PatternAgents/StickSoC/StickSoc/StickSoC_Left/eagleUp/eagleUp_StickSoc_Left_board_bottom.jpg

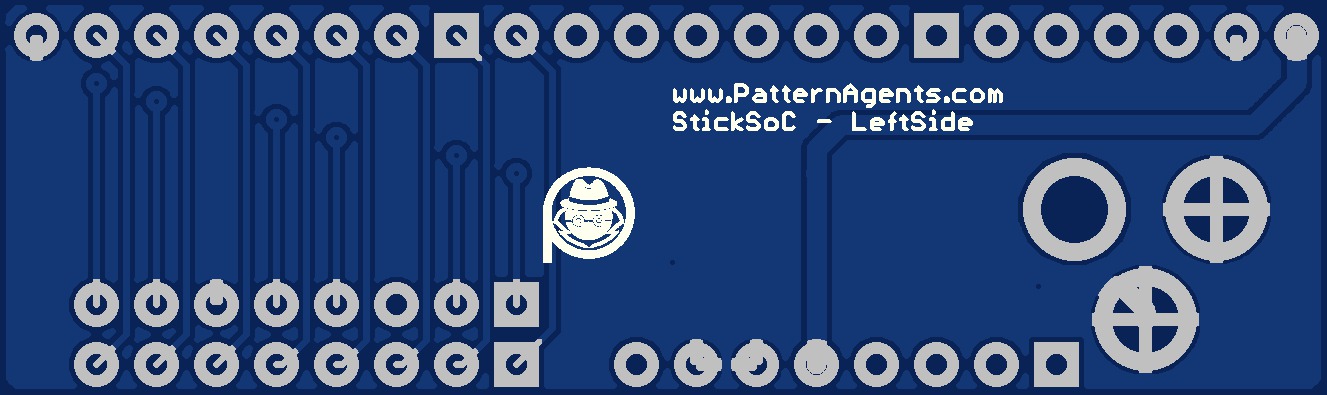
StickSoc/StickSoC_Left/eagleUp/eagleUp_StickSoc_Left_board_bottom.jpg
