PatternAgents/StickSoC/StickSoc/StickSoC_Left/eagleUp/eagleUp_StickSoc_Left_board_top.jpg

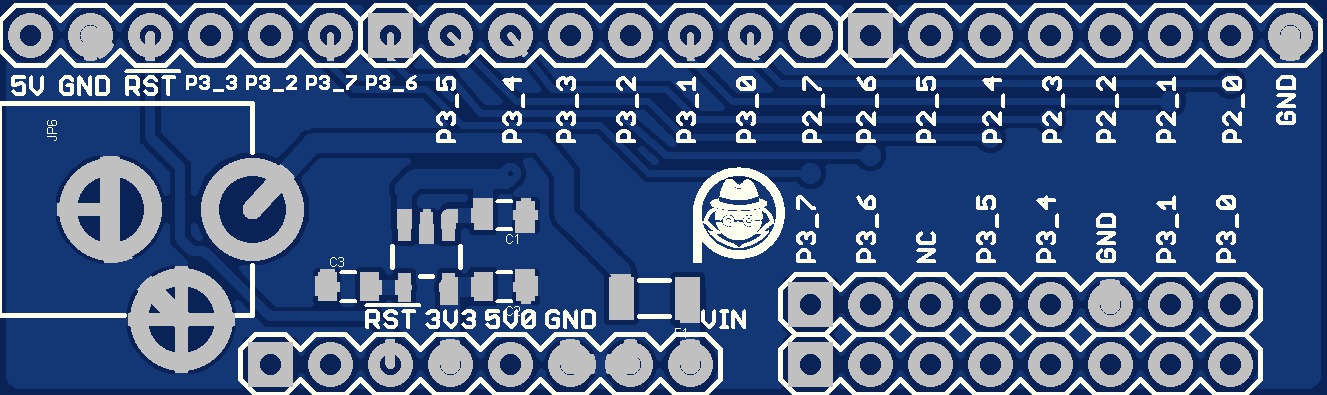
StickSoc/StickSoC_Left/eagleUp/eagleUp_StickSoc_Left_board_top.jpg
