PatternAgents/StickSoC/StickSoc/StickSoC_Left/images/StickSoC_Left_bot.png

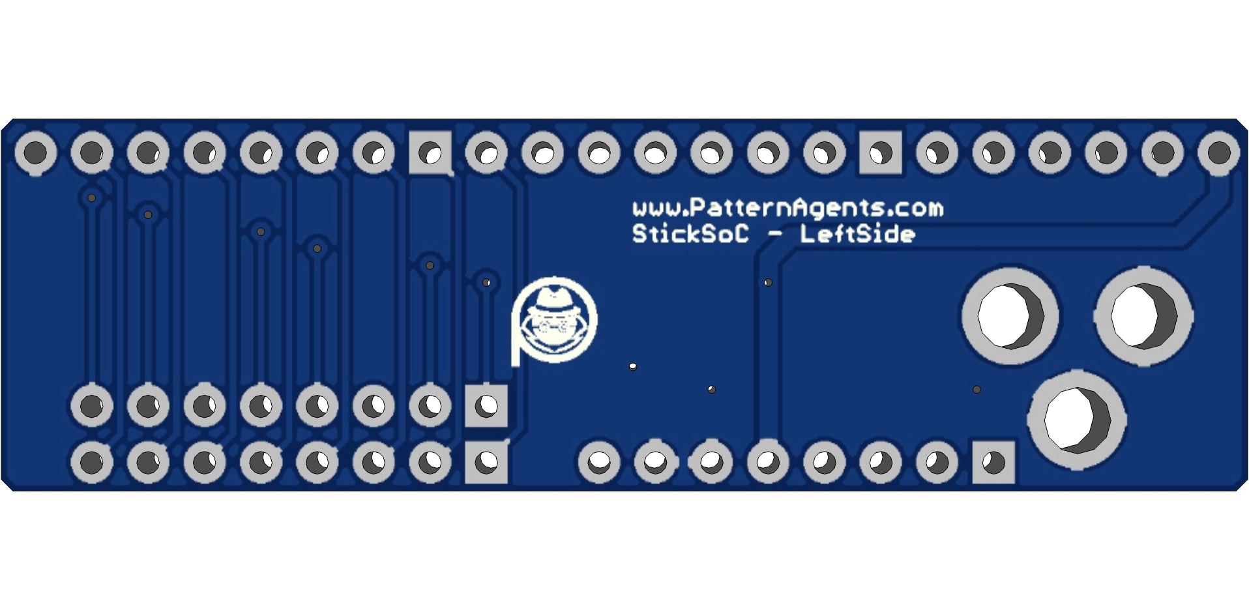
StickSoc/StickSoC_Left/images/StickSoC_Left_bot.png
