PatternAgents/StickSoC/StickSoc/StickSoc_Right/eagleUp/eagleUp_StickSoc_Right_board_bottom.jpg

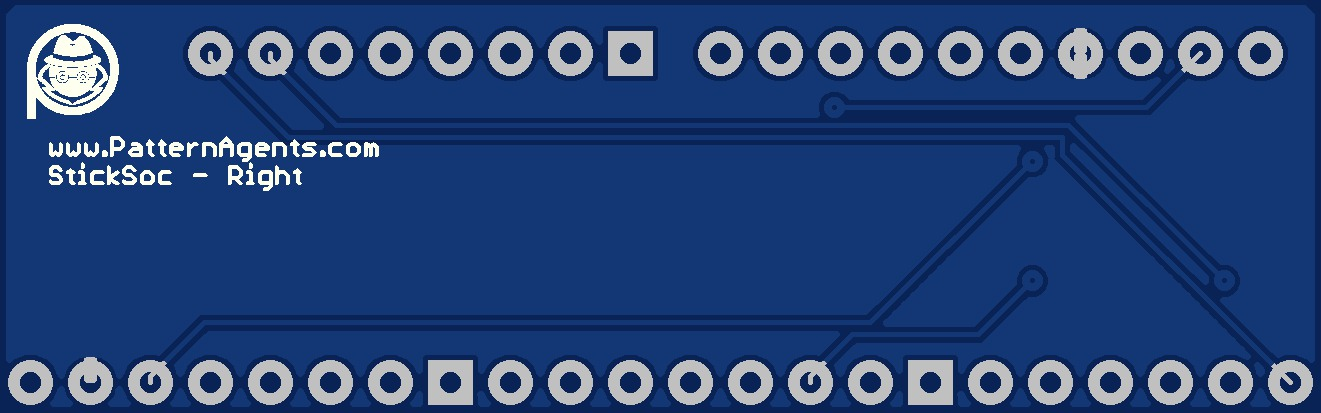
StickSoc/StickSoc_Right/eagleUp/eagleUp_StickSoc_Right_board_bottom.jpg
