PatternAgents/StickSoC/StickSoc/StickSoc_Right/eagleUp/eagleUp_StickSoc_Right_board_top.jpg

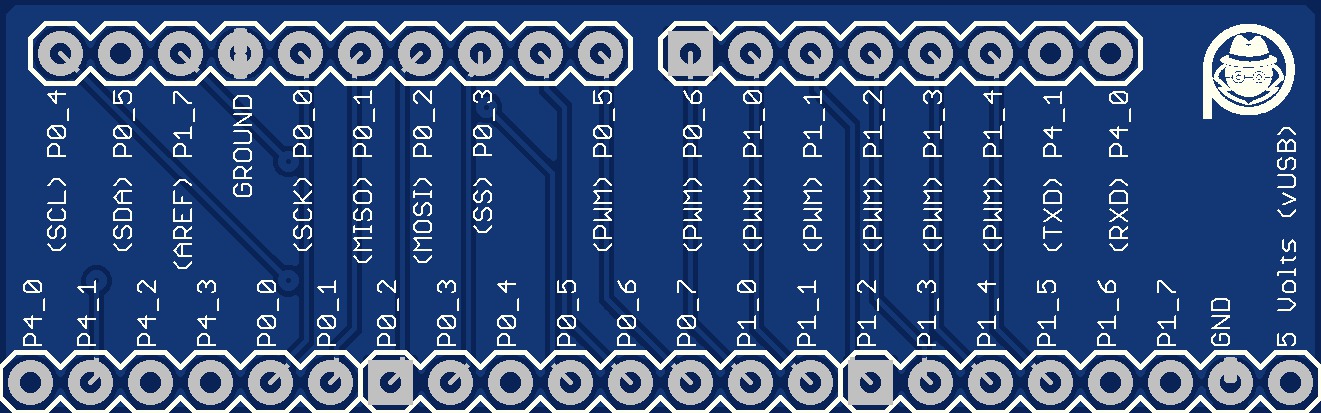
StickSoc/StickSoc_Right/eagleUp/eagleUp_StickSoc_Right_board_top.jpg
