PatternAgents/StickSoC/StickSoc/StickSoc_Right/images/StickSoC_Right_bot.png

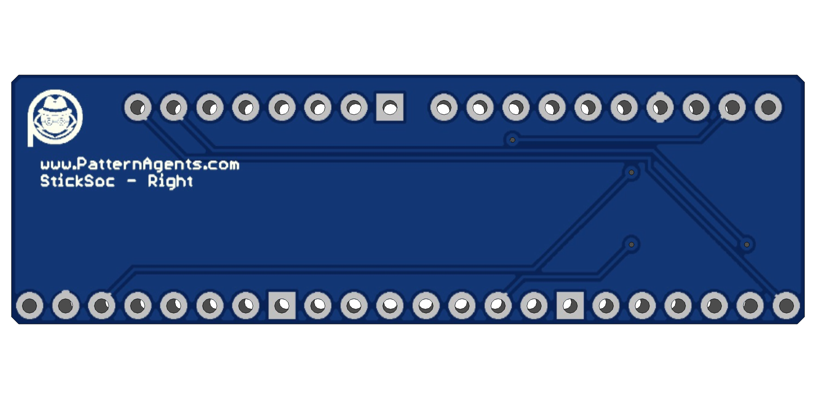
StickSoc/StickSoc_Right/images/StickSoC_Right_bot.png
